alexminator/ALT_nano/src/draw.h

void clean()
{
      lcd.setCursor(16, 1);
      lcd.print("    ");
      lcd.setCursor(16, 2);
      lcd.print("    ");
      lcd.setCursor(16, 3);
      lcd.print("    ");
}

void empty()
{
      // vacio
      draw->registerTank(0, WLe);
      draw->registerTank(1, WRe);
      draw->registerTank(2, WLBe);
      draw->registerTank(3, WRBe);
      clean();
      // wall left
      lcd.setCursor(16, 1);
      draw->drawTank(WLe);
      lcd.setCursor(16, 2);
      draw->drawTank(WLe);
      lcd.setCursor(16, 3);
      draw->drawTank(WLBe);
      // bottom
      lcd.setCursor(17, 3);
      lcd.write("_");
      lcd.setCursor(18, 3);
      lcd.write("_");
      // wall rigth
      lcd.setCursor(19, 1);
      draw->drawTank(WRe);
      lcd.setCursor(19, 2);
      draw->drawTank(WRe);
      lcd.setCursor(19, 3);
      draw->drawTank(WRBe);
}

void ten()
{
      // lleno 10%
      draw->registerTank(0, WLe);
      draw->registerTank(1, WRe);
      draw->registerTank(2, BL10);
      draw->registerTank(3, BR10);
      draw->registerTank(4, BC10);
      clean();
      // wall left
      lcd.setCursor(16, 1);
      draw->drawTank(WLe);
      lcd.setCursor(16, 2);
      draw->drawTank(WLe);
      lcd.setCursor(16, 3);
      draw->drawTank(BL10);
      // bottom
      lcd.setCursor(17, 3);
      draw->drawTank(BC10);
      lcd.setCursor(18, 3);
      draw->drawTank(BC10);
      // wall rigth
      lcd.setCursor(19, 1);
      draw->drawTank(WRe);
      lcd.setCursor(19, 2);
      draw->drawTank(WRe);
      lcd.setCursor(19, 3);
      draw->drawTank(BR10);
}

void twenty()
{
      // lleno 20%
      draw->registerTank(0, WLe);
      draw->registerTank(1, WRe);
      draw->registerTank(2, BL20);
      draw->registerTank(3, BR20);
      draw->registerTank(4, BC20);
      clean();
      // wall left
      lcd.setCursor(16, 1);
      draw->drawTank(WLe);
      lcd.setCursor(16, 2);
      draw->drawTank(WLe);
      lcd.setCursor(16, 3);
      draw->drawTank(BL20);
      // bottom
      lcd.setCursor(17, 3);
      draw->drawTank(BC20);
      lcd.setCursor(18, 3);
      draw->drawTank(BC20);
      // wall rigth
      lcd.setCursor(19, 1);
      draw->drawTank(WRe);
      lcd.setCursor(19, 2);
      draw->drawTank(WRe);
      lcd.setCursor(19, 3);
      draw->drawTank(BR20);
}

void thirty()
{
      // lleno 30%
      draw->registerTank(0, WLe);
      draw->registerTank(1, WRe);
      draw->registerTank(2, BL30);
      draw->registerTank(3, BR30);
      draw->registerTank(4, BC30);
      clean();
      // wall left
      lcd.setCursor(16, 1);
      draw->drawTank(WLe);
      lcd.setCursor(16, 2);
      draw->drawTank(WLe);
      lcd.setCursor(16, 3);
      draw->drawTank(BL30);
      // bottom
      lcd.setCursor(17, 3);
      draw->drawTank(BC30);
      lcd.setCursor(18, 3);
      draw->drawTank(BC30);
      // wall rigth
      lcd.setCursor(19, 1);
      draw->drawTank(WRe);
      lcd.setCursor(19, 2);
      draw->drawTank(WRe);
      lcd.setCursor(19, 3);
      draw->drawTank(BR30);
}

void forty()
{
      // lleno 40%
      draw->registerTank(0, WLe);
      draw->registerTank(1, WRe);
      draw->registerTank(2, WL48);
      draw->registerTank(3, WR48);
      draw->registerTank(4, C48);
      draw->registerTank(5, BL30);
      draw->registerTank(6, BR30);
      draw->registerTank(7, BC30);
      clean();
      // wall left
      lcd.setCursor(16, 1);
      draw->drawTank(WLe);
      lcd.setCursor(16, 2);
      draw->drawTank(WL48);
      lcd.setCursor(16, 3);
      draw->drawTank(BL30);
      // bottom
      lcd.setCursor(17, 3);
      draw->drawTank(BC30);
      lcd.setCursor(18, 3);
      draw->drawTank(BC30);
      lcd.setCursor(17, 2);
      draw->drawTank(C48);
      lcd.setCursor(18, 2);
      draw->drawTank(C48);
      // wall rigth
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
      lcd.setCursor(17, 2);
      lcd.write(0xFF);
      lcd.setCursor(18, 2);
      lcd.write(0xFF);
      // wall rigth
      lcd.setCursor(19, 1);
      draw->drawTank(WR61);
      lcd.setCursor(19, 2);
      draw->drawTank(WR70);
      lcd.setCursor(19, 3);
      draw->drawTank(BR30);
}
